vitaliyrenkas-rgb/UNIVERSAL-MOSFET-KEY-PCB/IMG/002.PNG

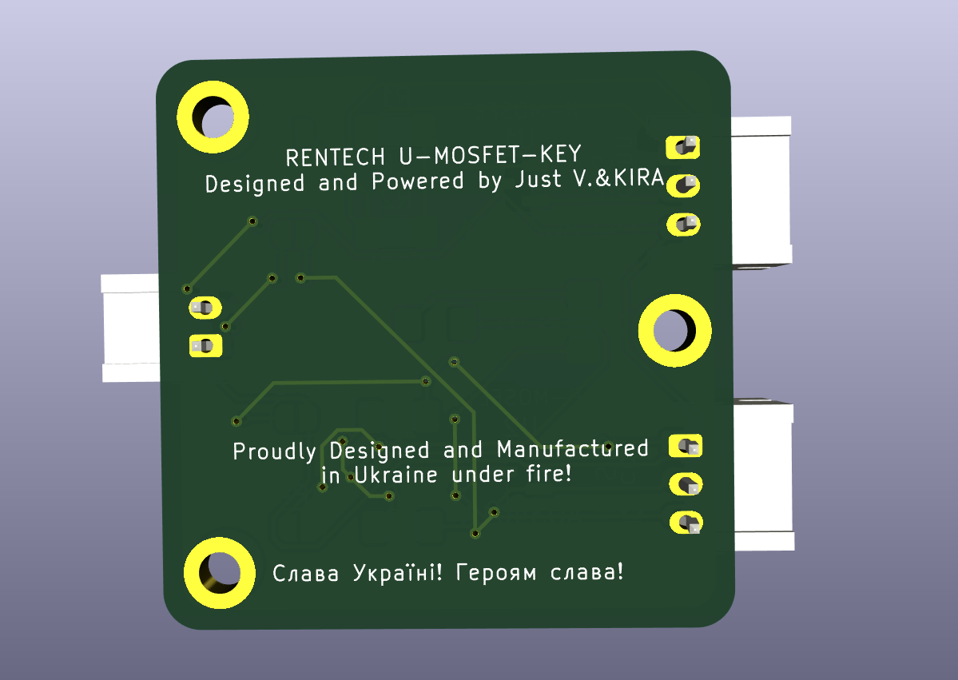
IMG/002.PNG
