vitaliyrenkas-rgb/UNIVERSAL-MOSFET-KEY-PCB/IMG/003.PNG

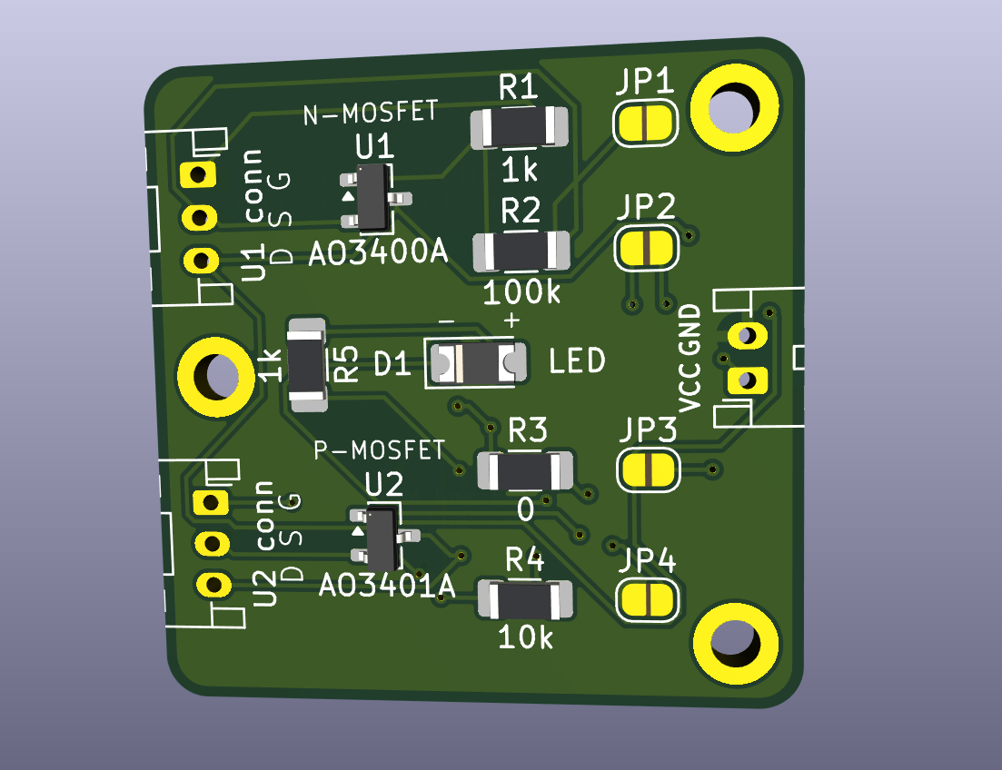
IMG/003.PNG
