vitaliyrenkas-rgb/UNIVERSAL-MOSFET-KEY-PCB/IMG/004.PNG

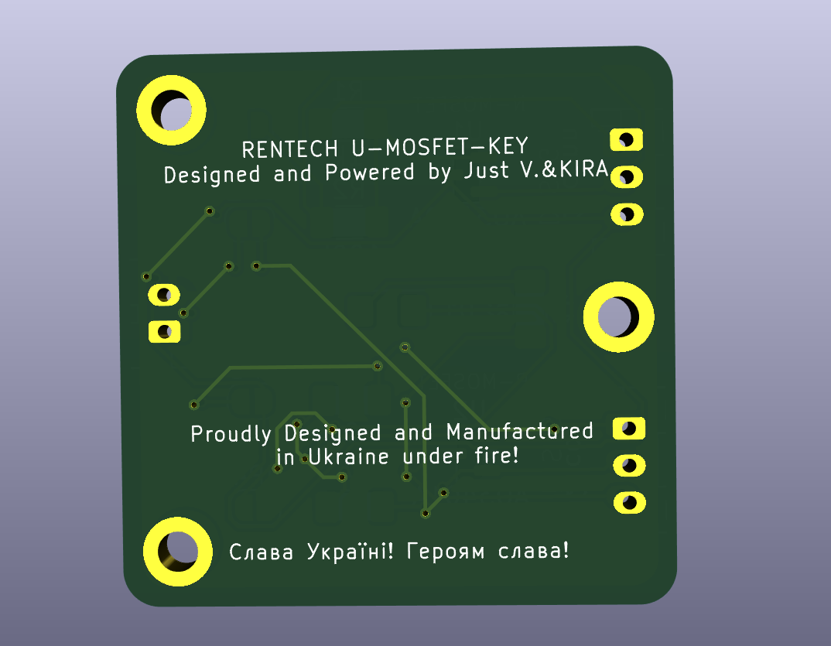
IMG/004.PNG
